andyshinn/kuberdoo/photos/IMG_20171010_163735.jpg

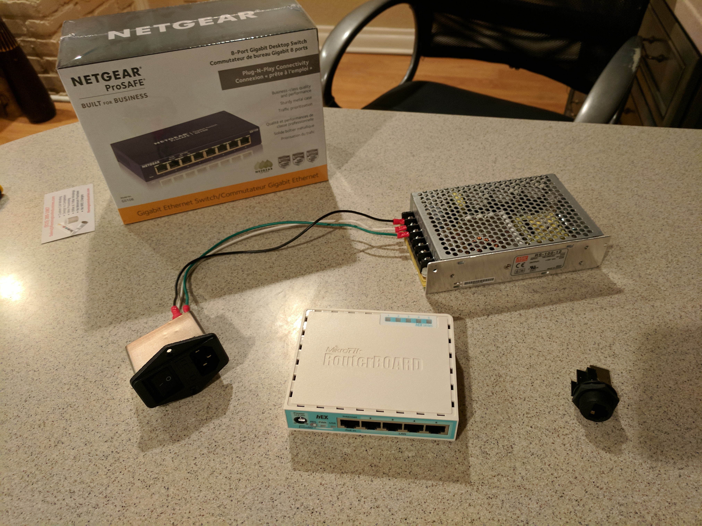
photos/IMG_20171010_163735.jpg
