andyshinn/kuberdoo/photos/IMG_20171011_145013.jpg

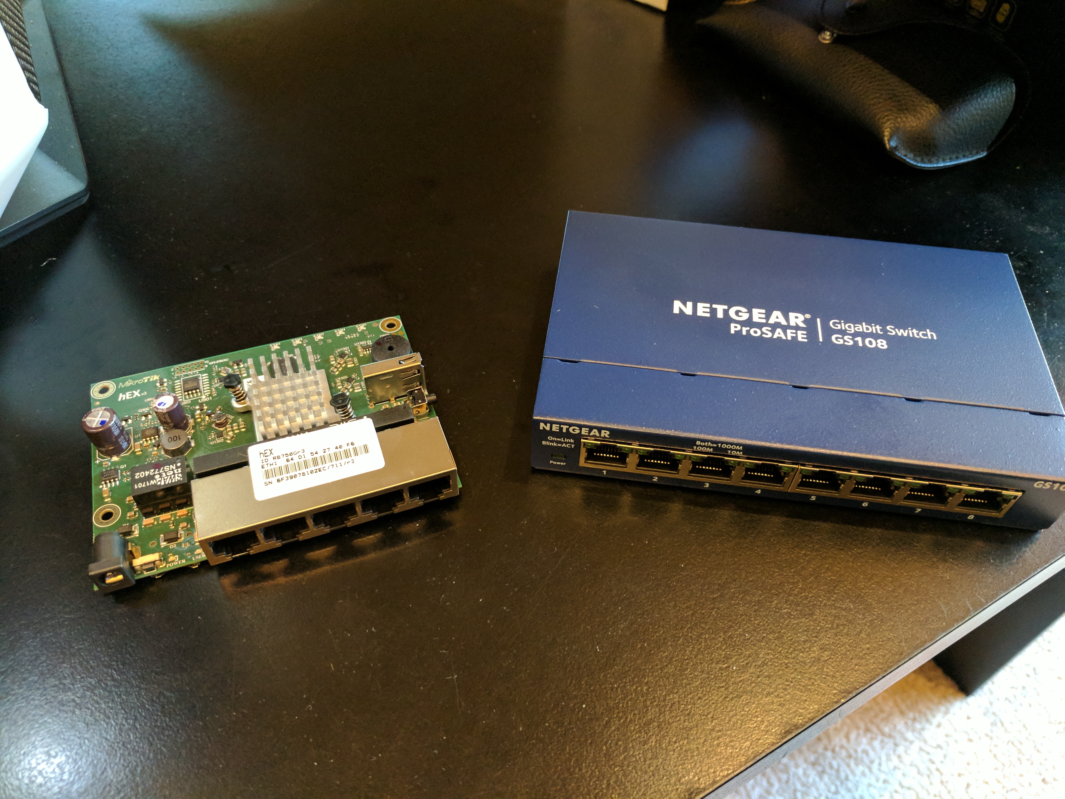
photos/IMG_20171011_145013.jpg
