andyshinn/kuberdoo/photos/IMG_20171011_145058.jpg

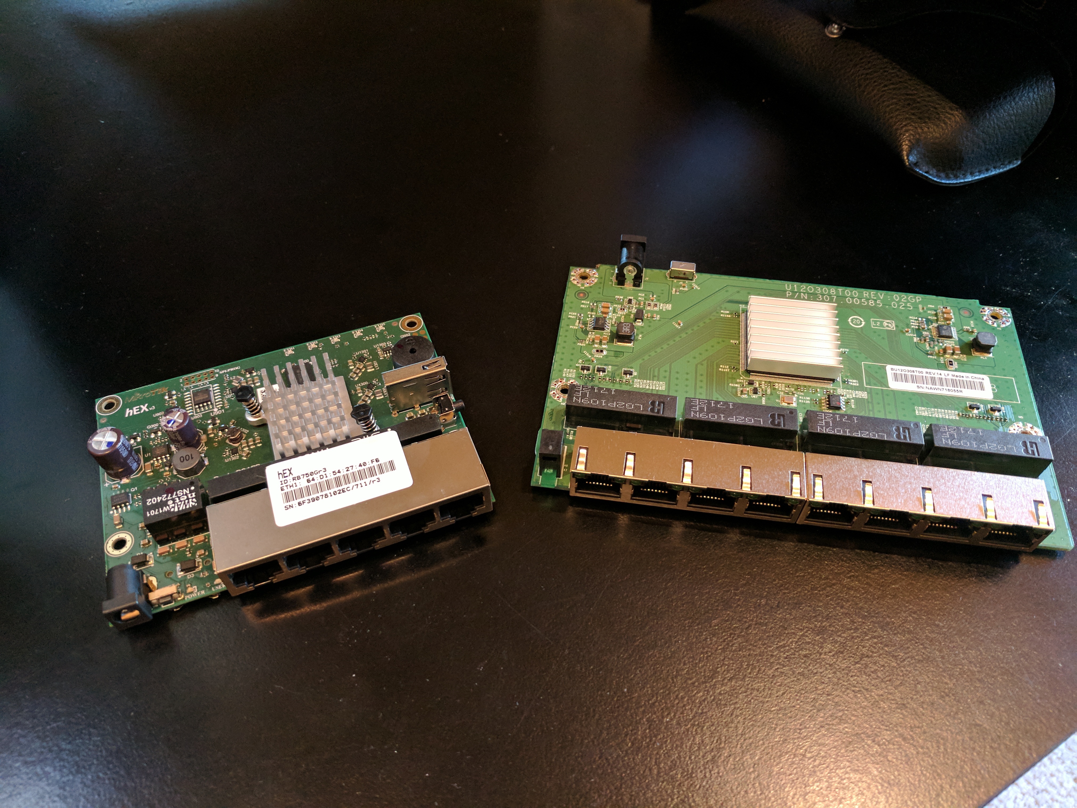
photos/IMG_20171011_145058.jpg
