andyshinn/kuberdoo/photos/IMG_20171011_181252.jpg

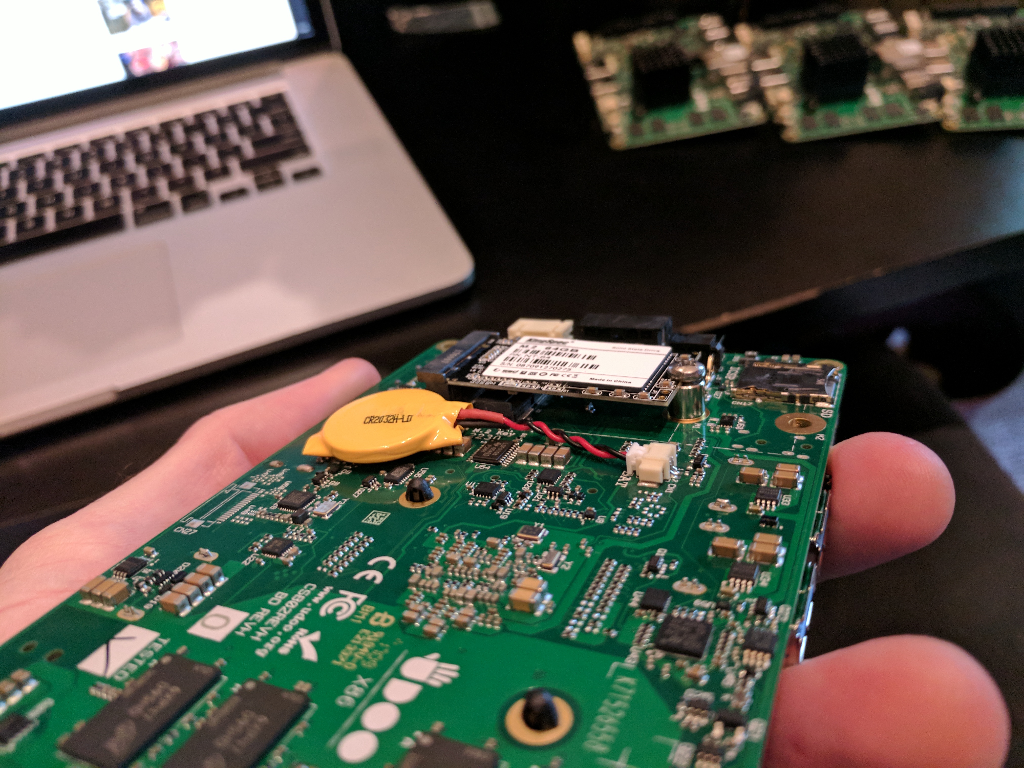
photos/IMG_20171011_181252.jpg
