andyshinn/kuberdoo/photos/IMG_20171011_182714.jpg

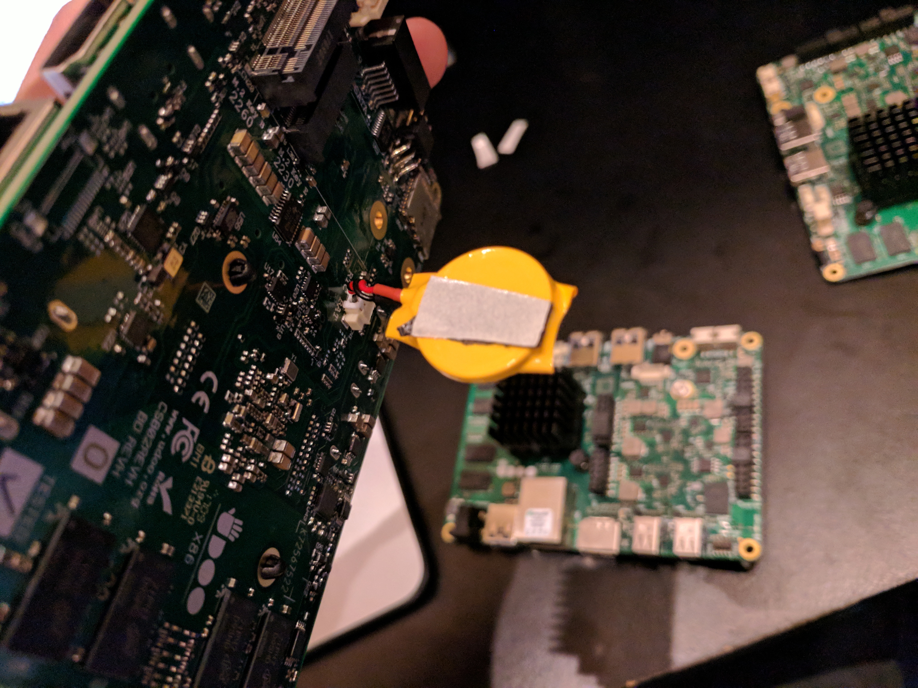
photos/IMG_20171011_182714.jpg
