andyshinn/kuberdoo/photos/IMG_20171023_182342.jpg

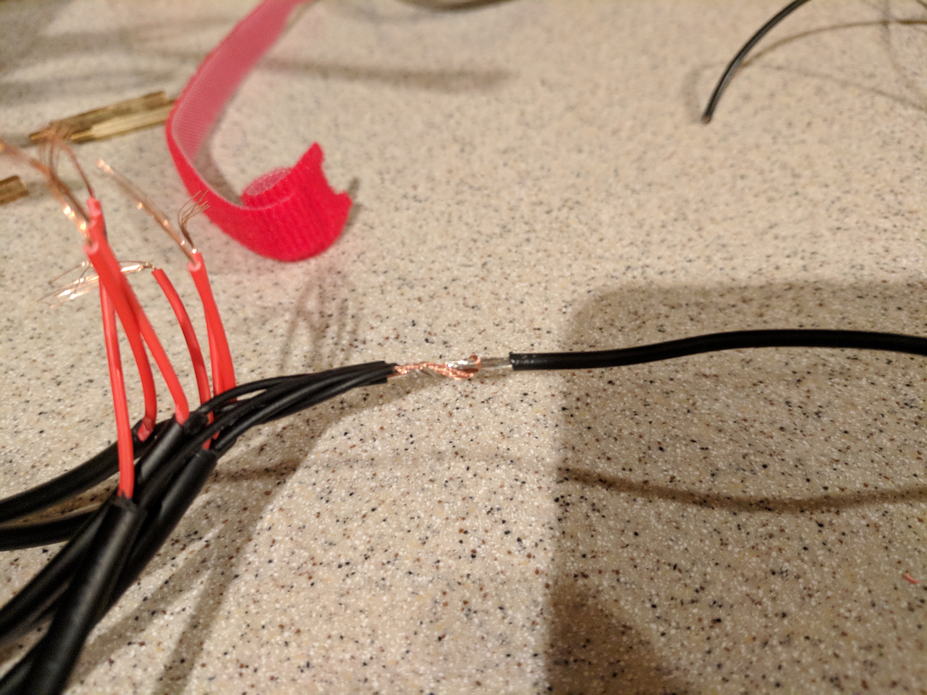
photos/IMG_20171023_182342.jpg
