andyshinn/kuberdoo/photos/IMG_20171023_183057.jpg

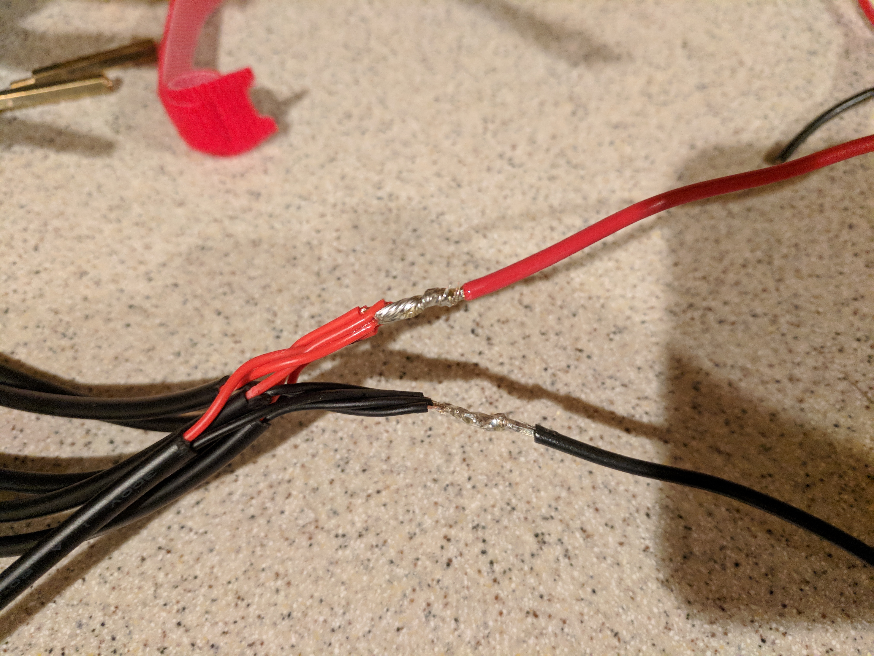
photos/IMG_20171023_183057.jpg
