andyshinn/kuberdoo/photos/IMG_20171023_183552.jpg

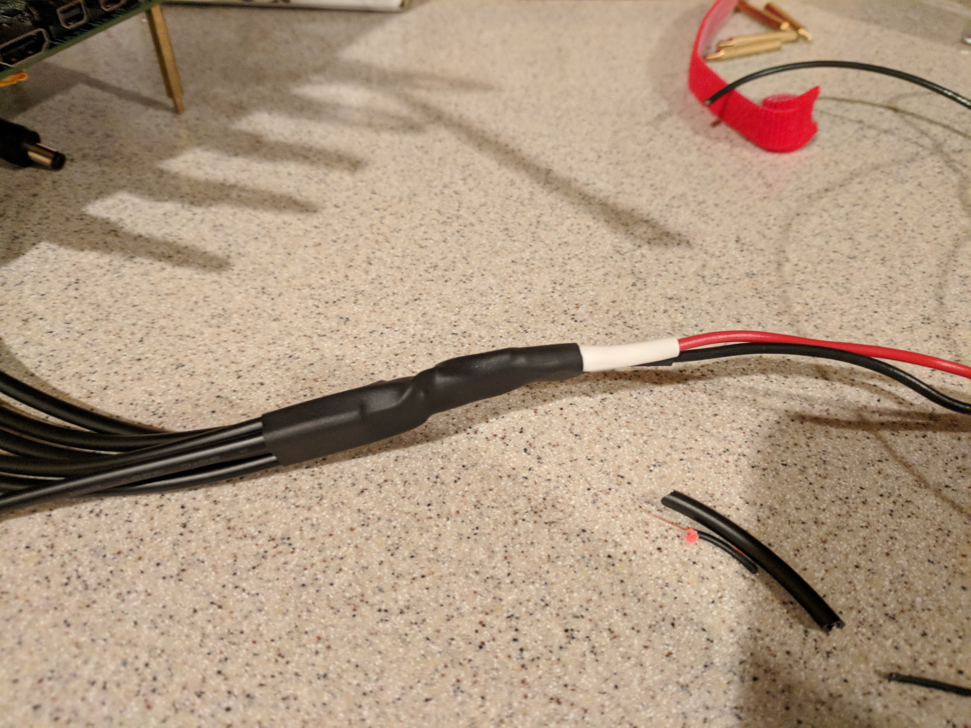
photos/IMG_20171023_183552.jpg
