andyshinn/kuberdoo/photos/IMG_20171024_130323.jpg

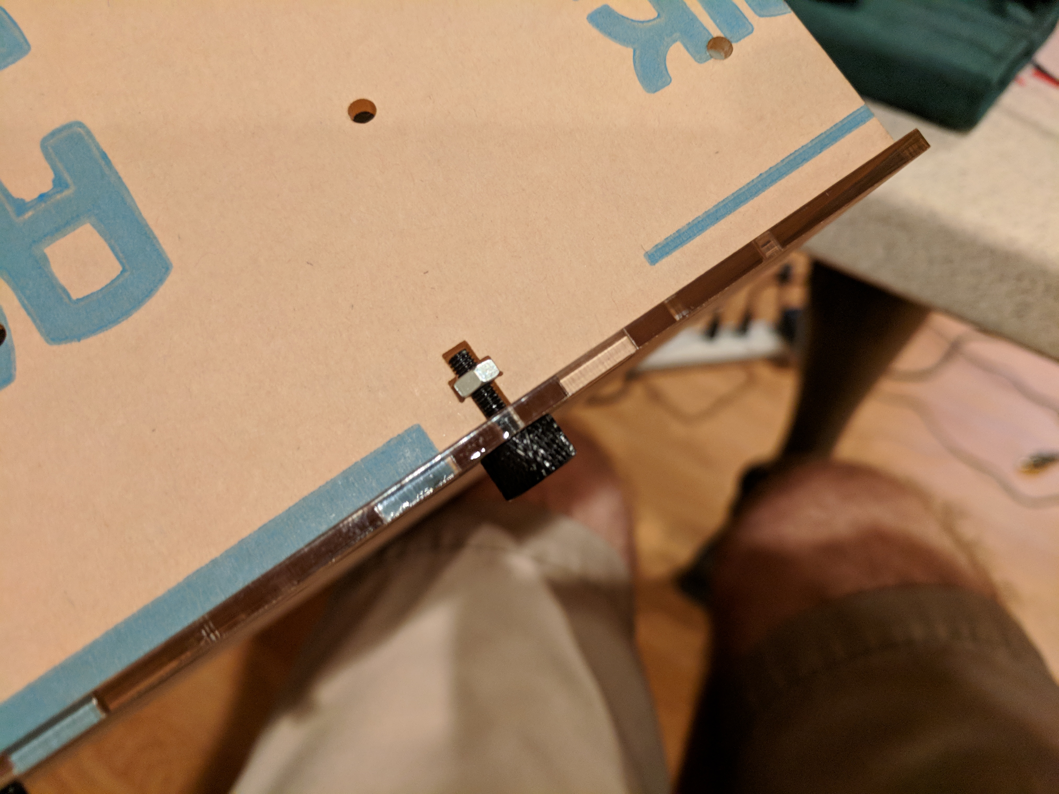
photos/IMG_20171024_130323.jpg
