andyshinn/kuberdoo/photos/IMG_20171024_144707.jpg

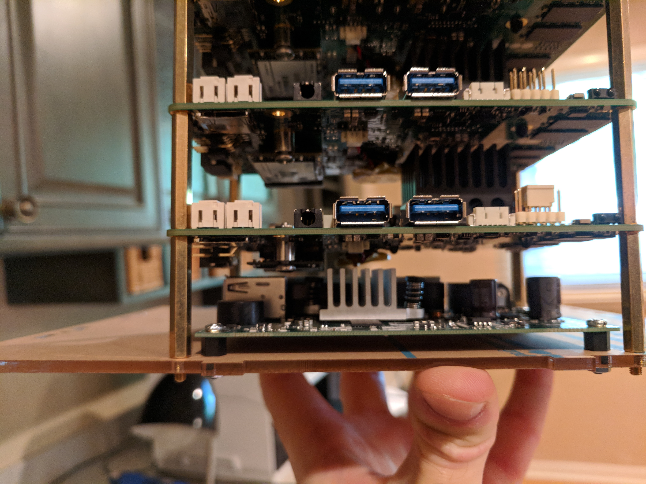
photos/IMG_20171024_144707.jpg
