andyshinn/kuberdoo/photos/IMG_20171024_145050.jpg

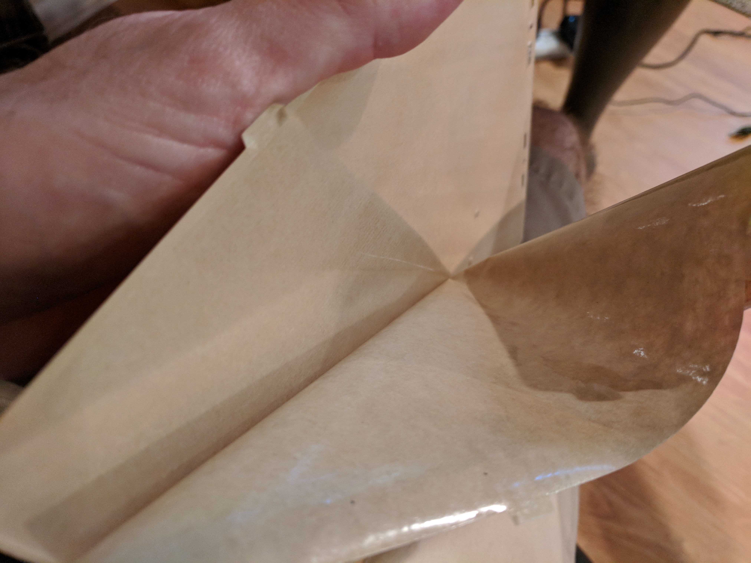
photos/IMG_20171024_145050.jpg
