andyshinn/kuberdoo/photos/IMG_20171024_145436.jpg

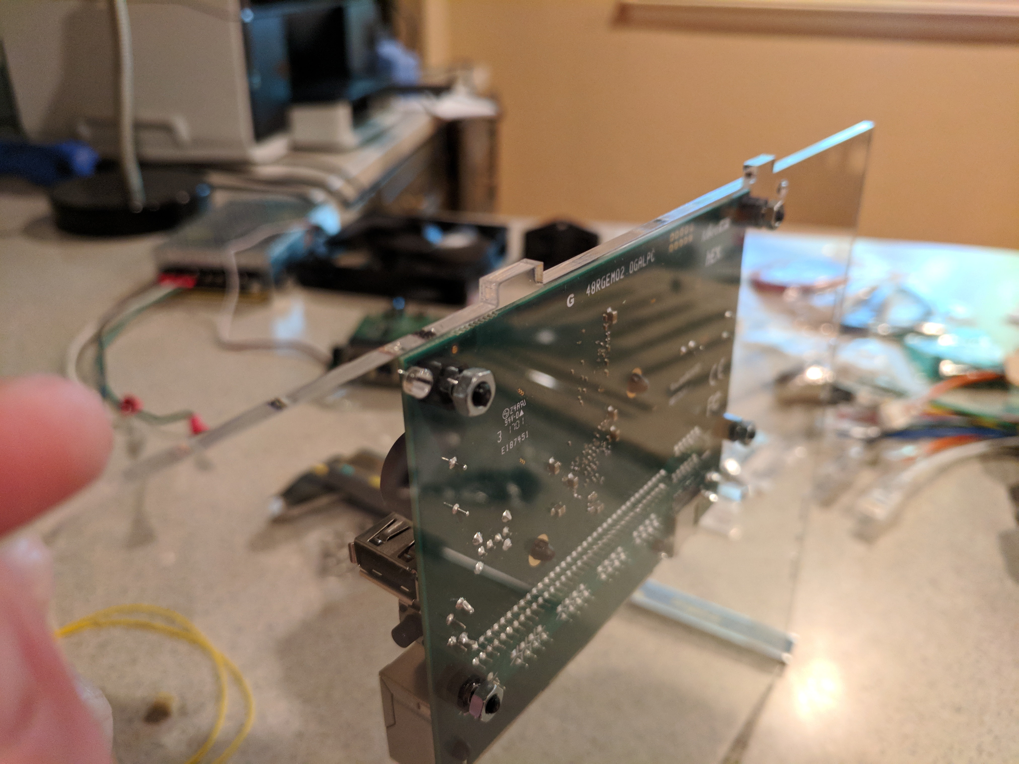
photos/IMG_20171024_145436.jpg
