andyshinn/kuberdoo/photos/IMG_20171024_145449.jpg

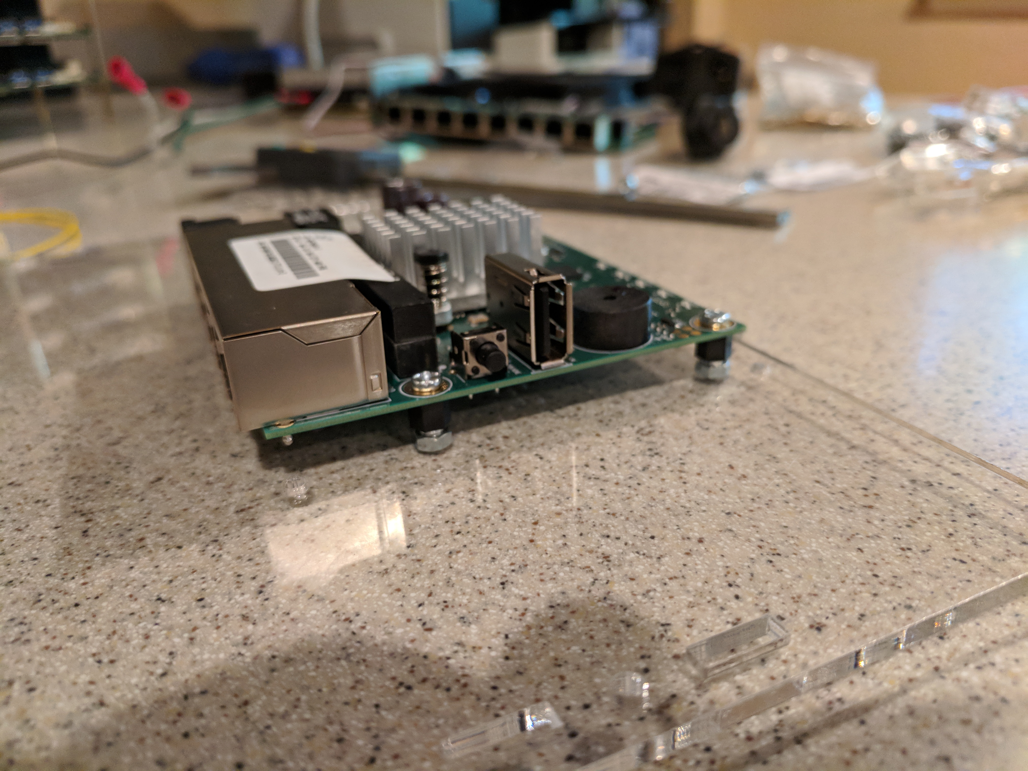
photos/IMG_20171024_145449.jpg
