andyshinn/kuberdoo/photos/IMG_20171024_152010.jpg

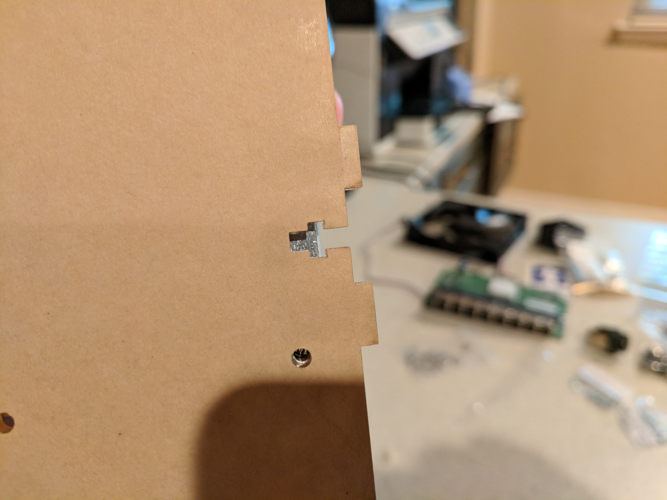
photos/IMG_20171024_152010.jpg
