andyshinn/kuberdoo/photos/IMG_20171024_160728.jpg

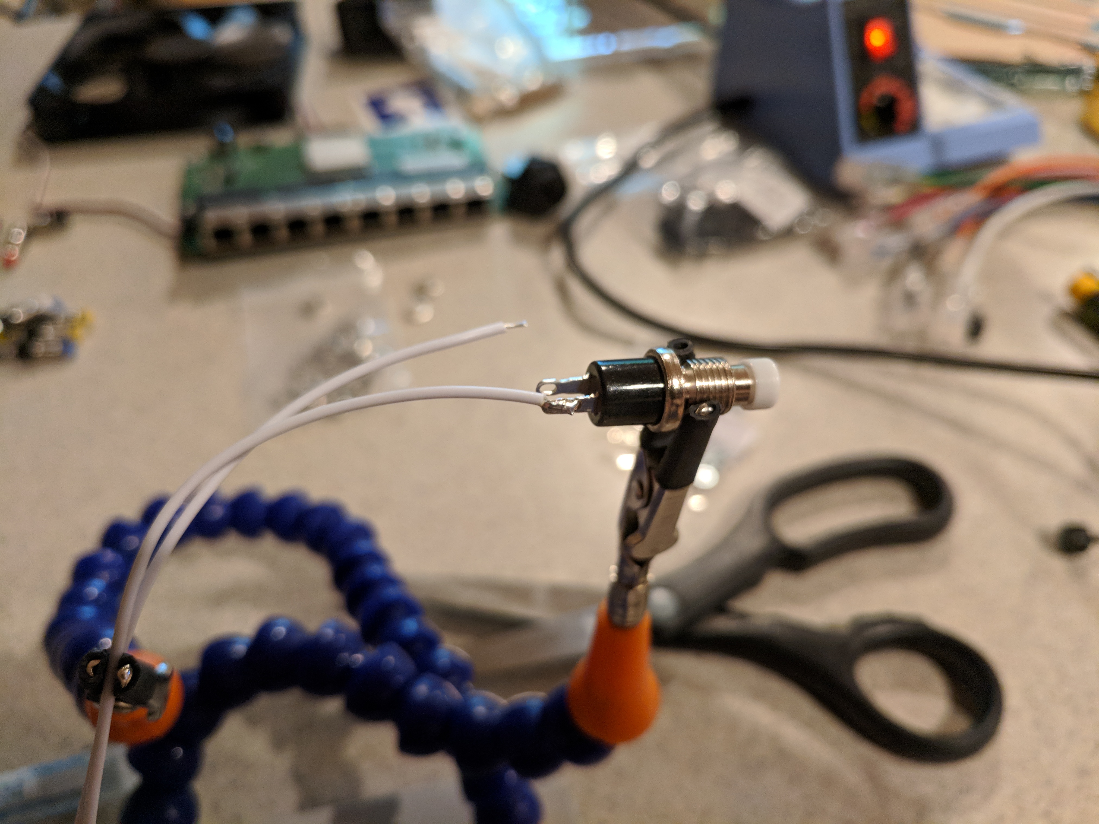
photos/IMG_20171024_160728.jpg
