andyshinn/kuberdoo/photos/IMG_20171024_161921.jpg

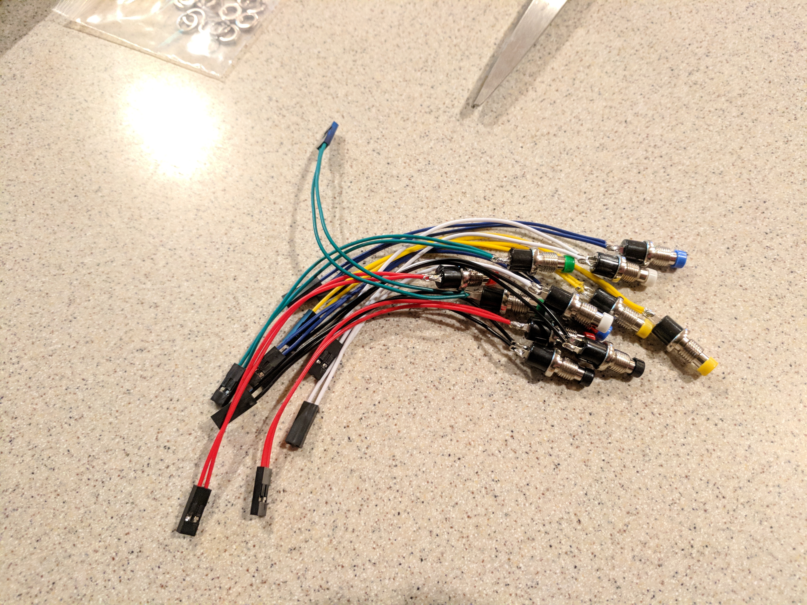
photos/IMG_20171024_161921.jpg
