andyshinn/kuberdoo/photos/IMG_20171024_163146.jpg

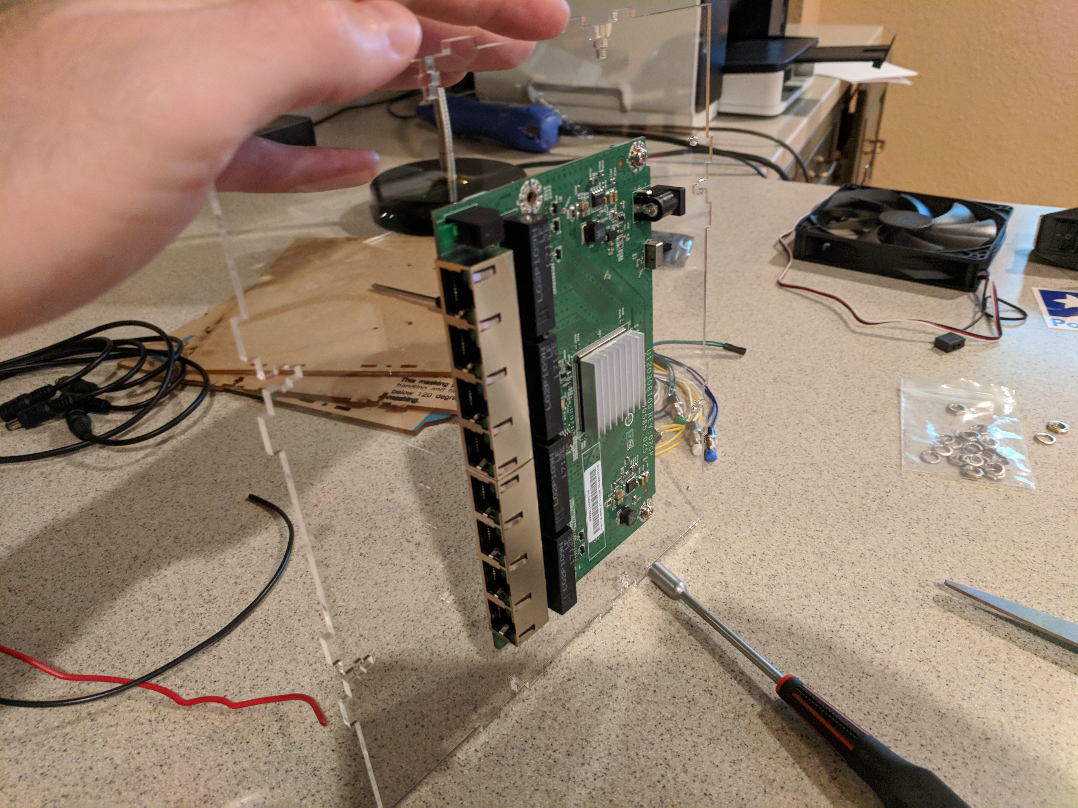
photos/IMG_20171024_163146.jpg
