andyshinn/kuberdoo/photos/IMG_20171024_163850.jpg

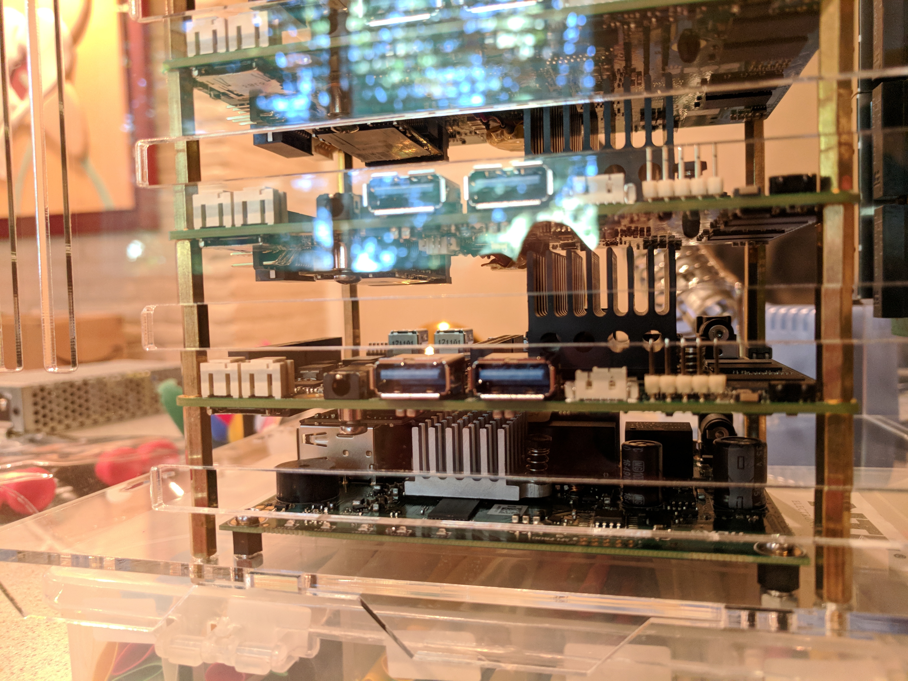
photos/IMG_20171024_163850.jpg
