andyshinn/kuberdoo/photos/IMG_20171024_163856.jpg

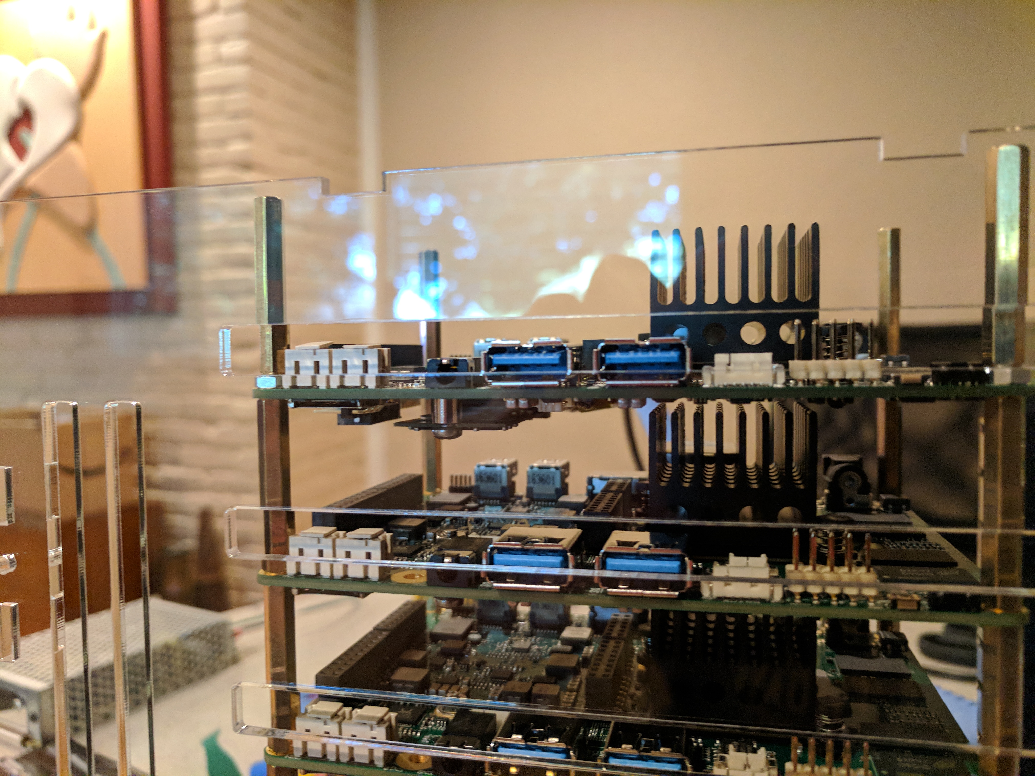
photos/IMG_20171024_163856.jpg
