andyshinn/kuberdoo/photos/IMG_20171024_164758.jpg

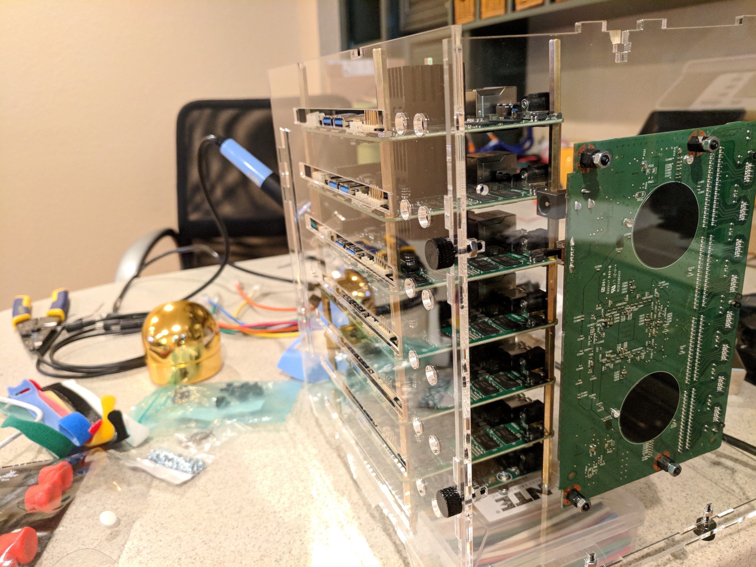
photos/IMG_20171024_164758.jpg
