andyshinn/kuberdoo/photos/IMG_20171024_222128.jpg

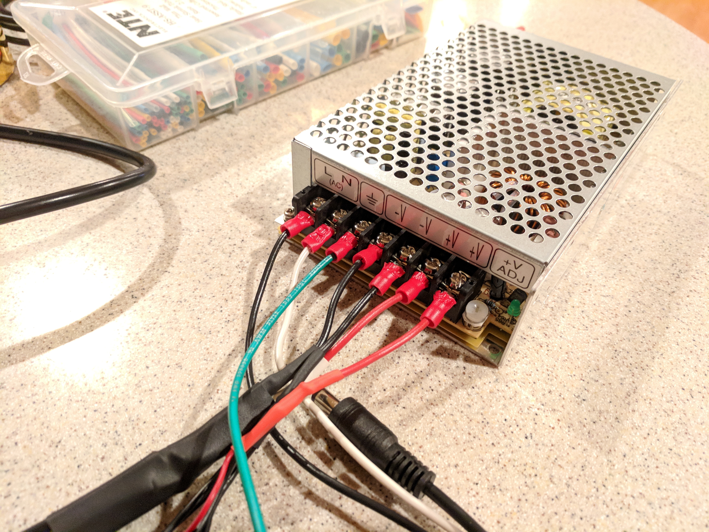
photos/IMG_20171024_222128.jpg
