andyshinn/kuberdoo/photos/IMG_20171024_223846.jpg

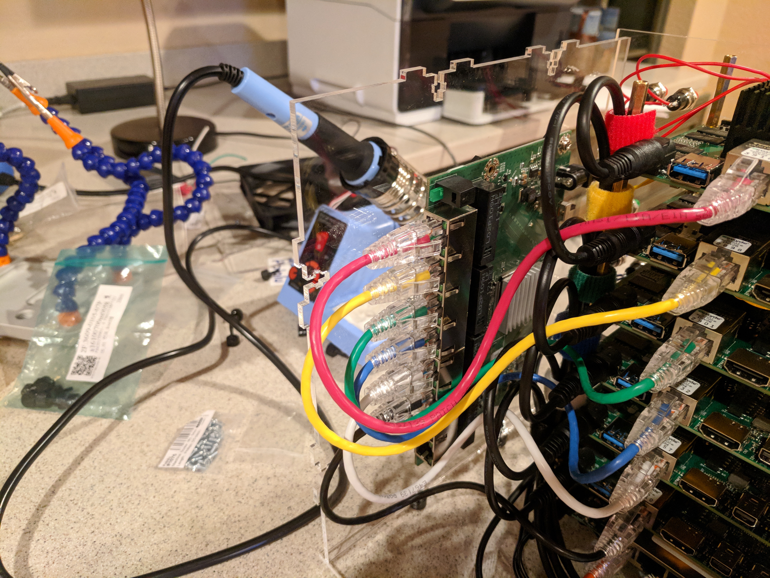
photos/IMG_20171024_223846.jpg
