andyshinn/kuberdoo/photos/IMG_20171024_223857.jpg

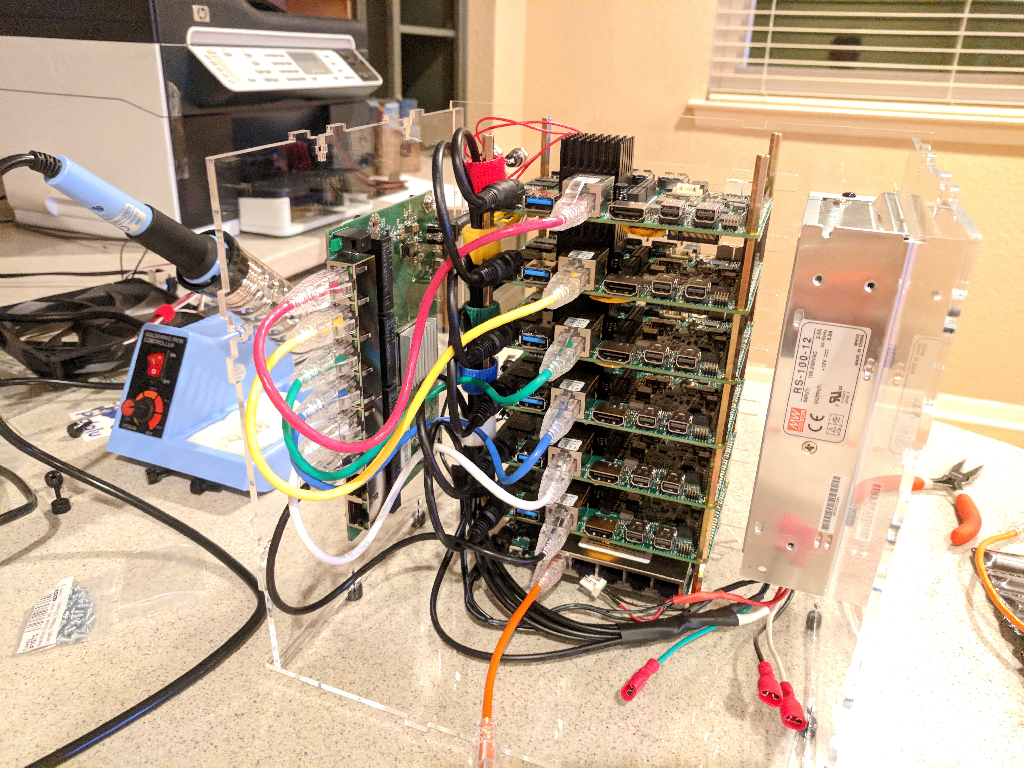
photos/IMG_20171024_223857.jpg
