andyshinn/kuberdoo/photos/IMG_20171024_224913.jpg

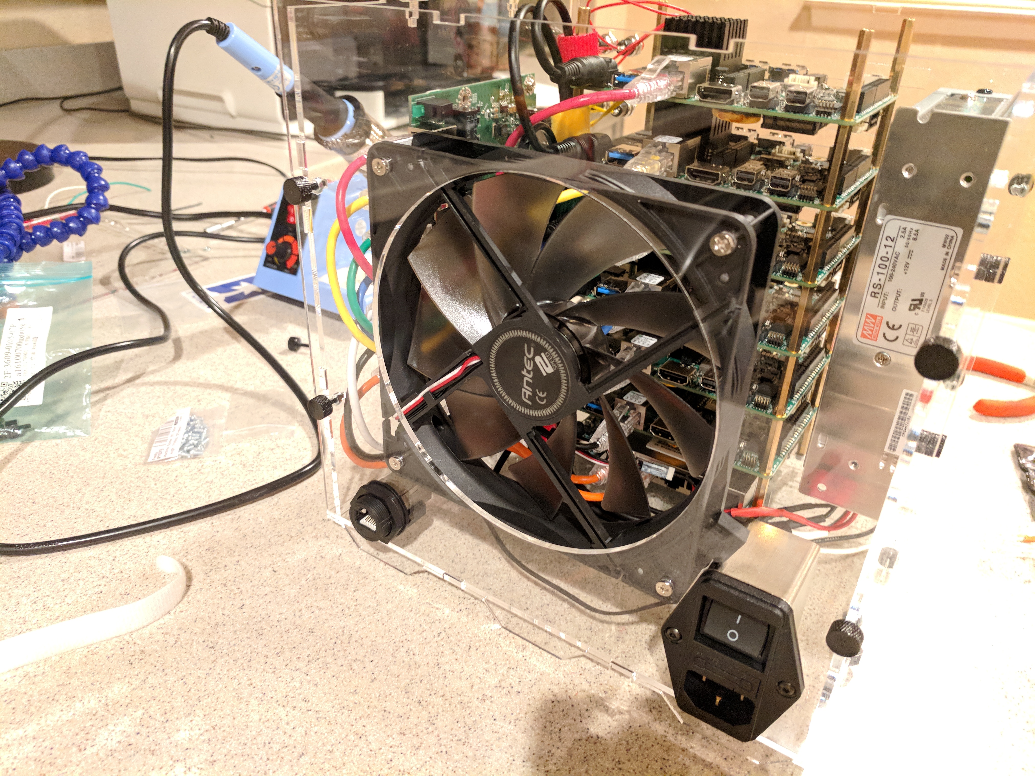
photos/IMG_20171024_224913.jpg
