andyshinn/kuberdoo/photos/IMG_20171024_224921.jpg

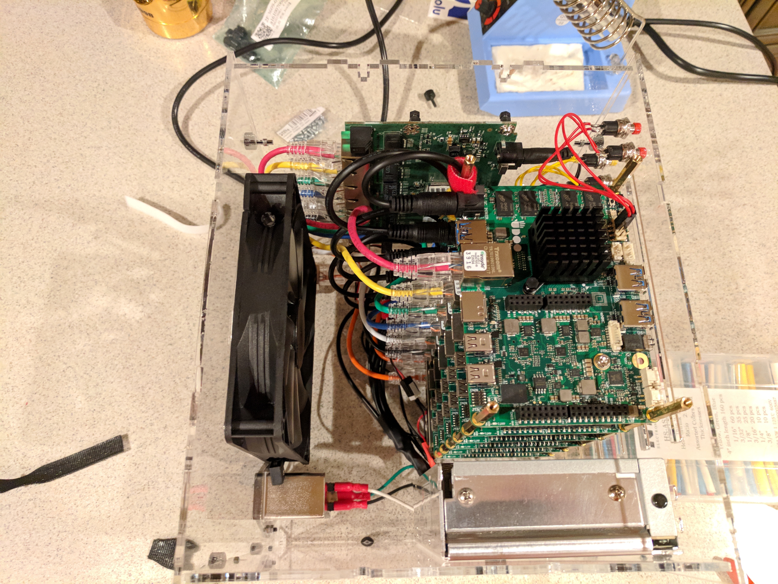
photos/IMG_20171024_224921.jpg
