andyshinn/kuberdoo/photos/IMG_20171024_232211.jpg

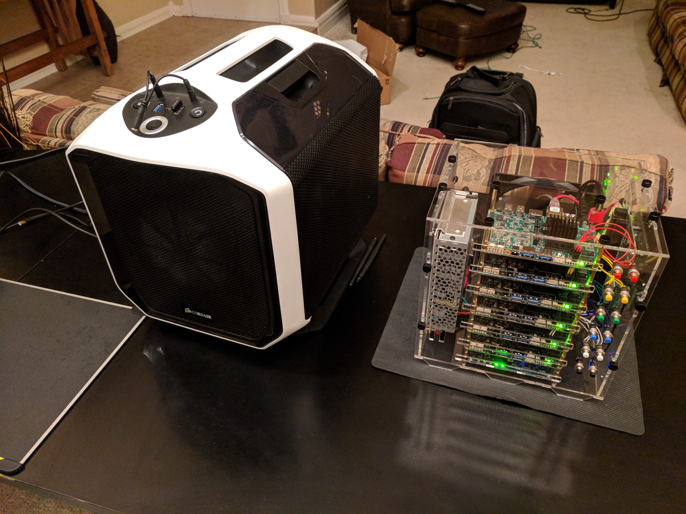
photos/IMG_20171024_232211.jpg
