andyshinn/kuberdoo/photos/IMG_20171024_232223.jpg

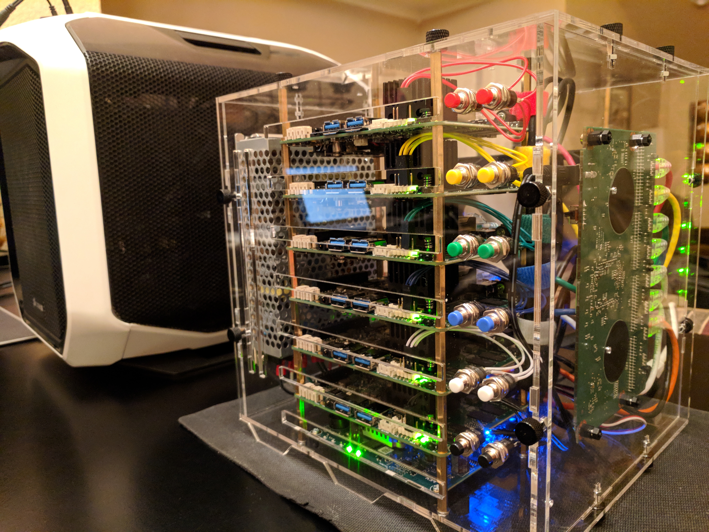
photos/IMG_20171024_232223.jpg
