andyshinn/kuberdoo/photos/IMG_20171024_232300.jpg

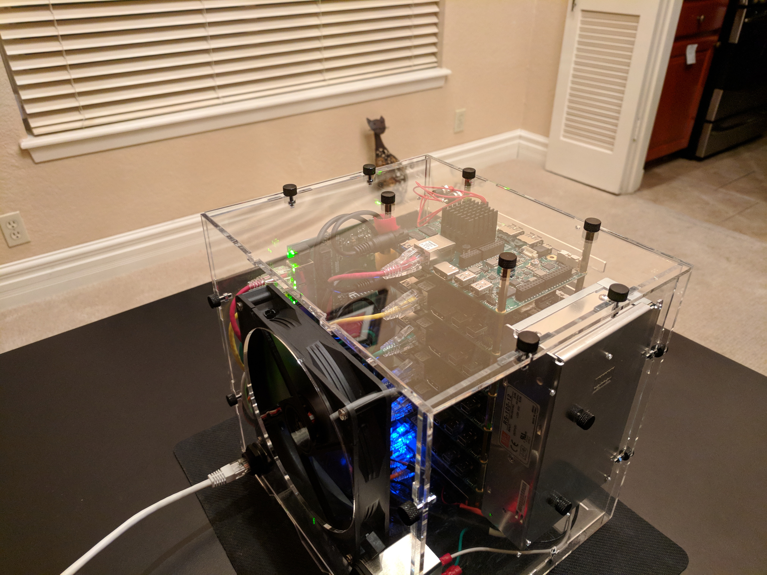
photos/IMG_20171024_232300.jpg
